CedarGroveStudios/RetroMeter/docs/input output ratio.pdf

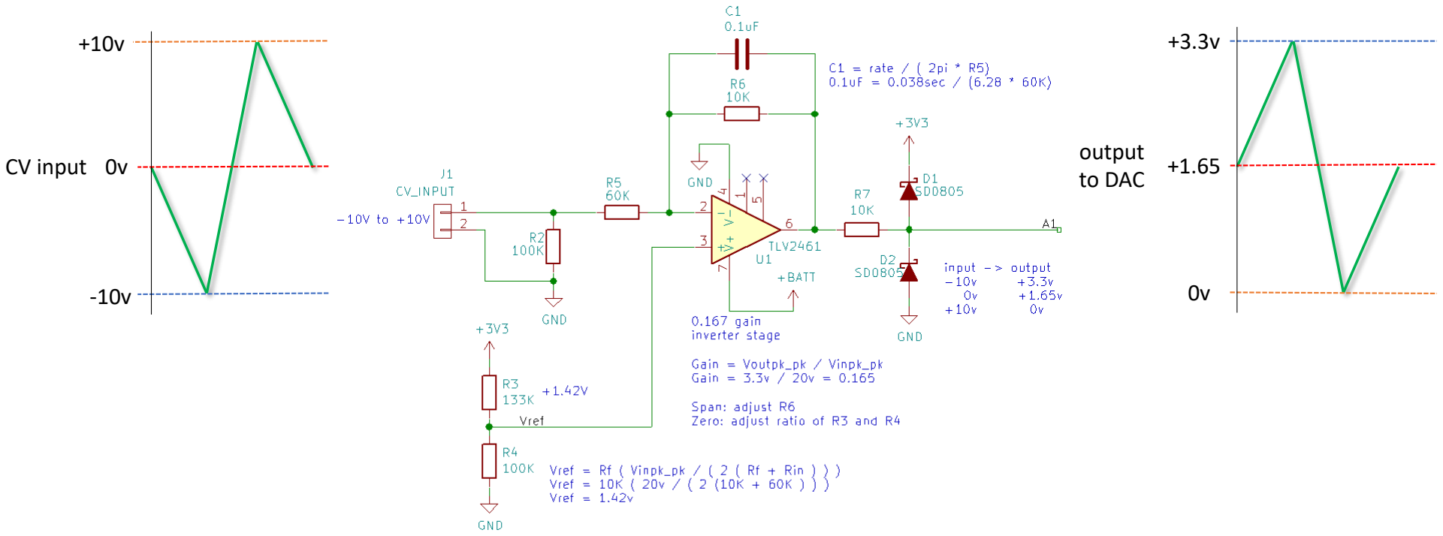
[picture p24: page 1]

+3.3v

+1.65

0v

output
to DAC

-10v

0v

+10v

CV input
