CedarGroveStudios/RetroMeter/docs/retro meter v02.pdf

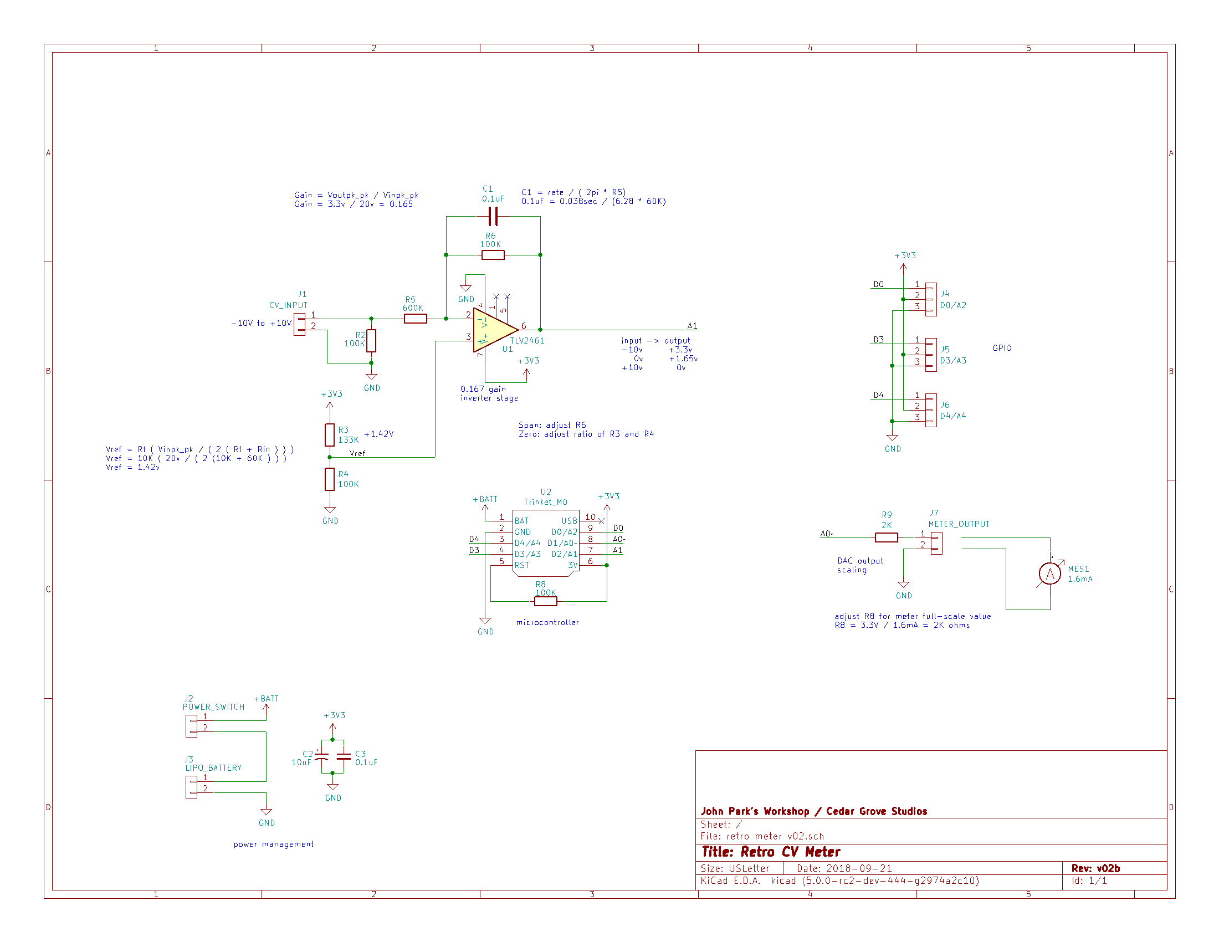
[picture p25: page 1]
