CedarGroveStudios/RetroMeter/docs/2018-08-17 retro meter study/schematic v01.pdf

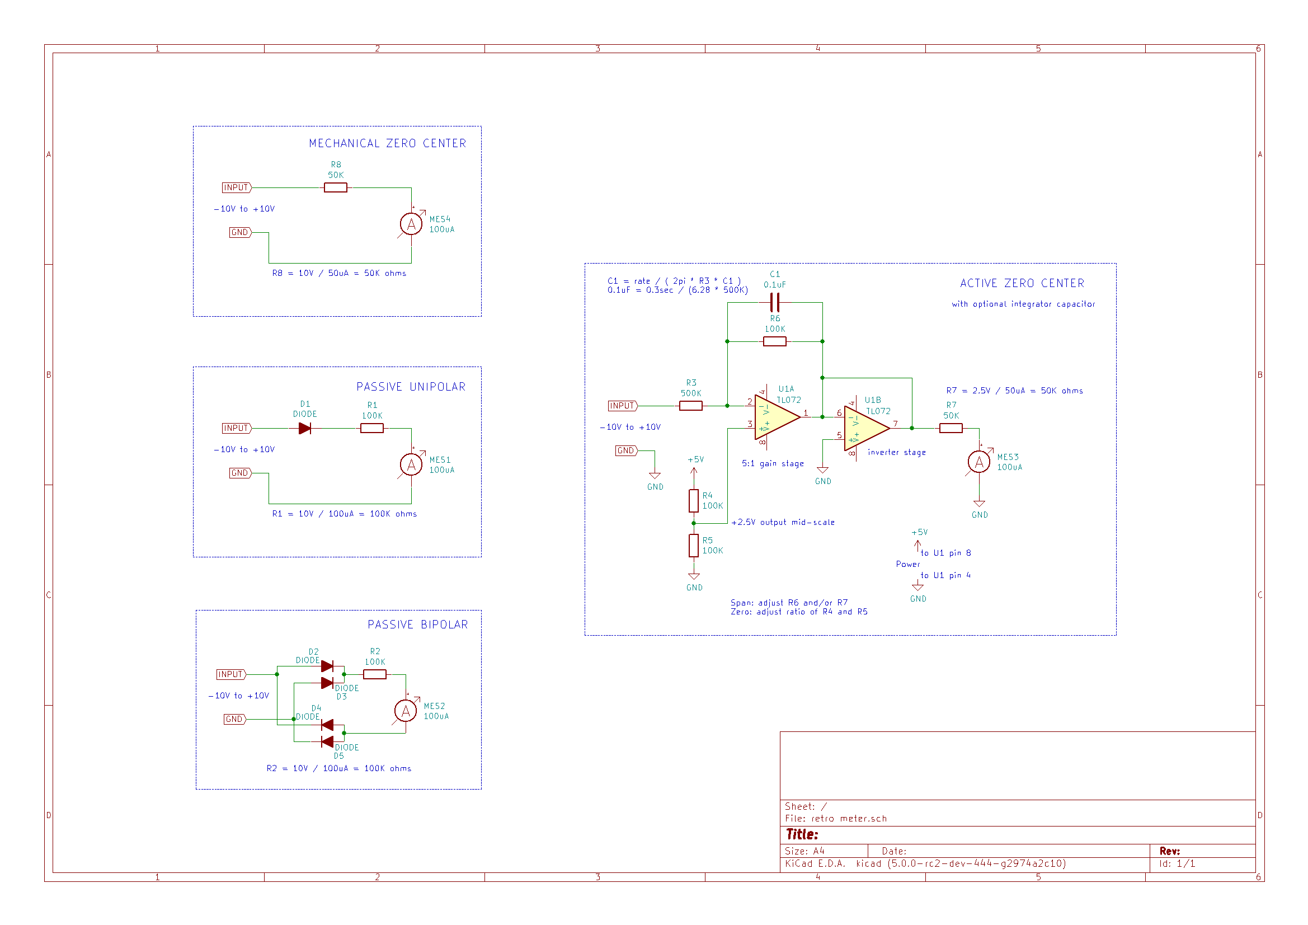
[picture p26: page 1]
