CedarGroveStudios/RetroMeter/docs/2018-08-17 retro meter study/original meter circuit.PNG

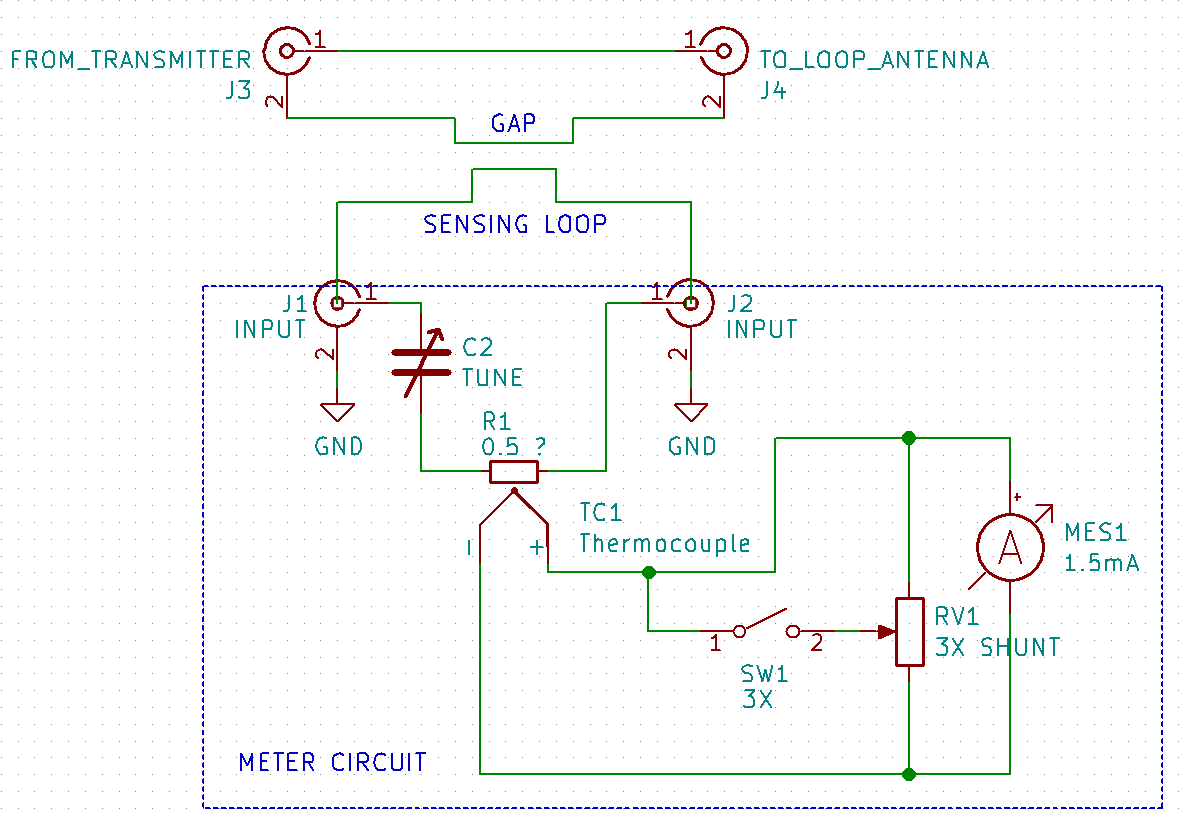
docs/2018-08-17 retro meter study/original meter circuit.PNG
