CedarGroveStudios/RetroMeter/docs/input output ratio.png

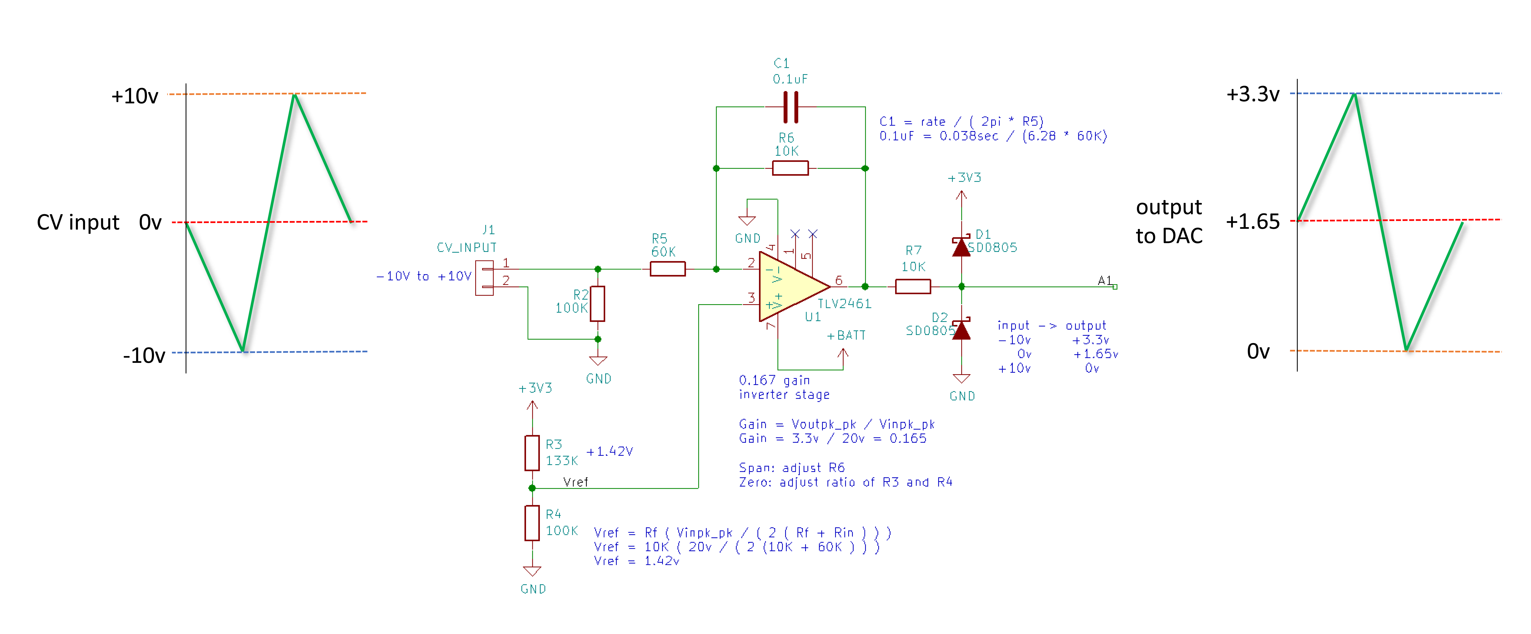
docs/input output ratio.png
