CedarGroveStudios/RetroMeter/PCB Rover/2018-08-20 analog Trinket sub front.png

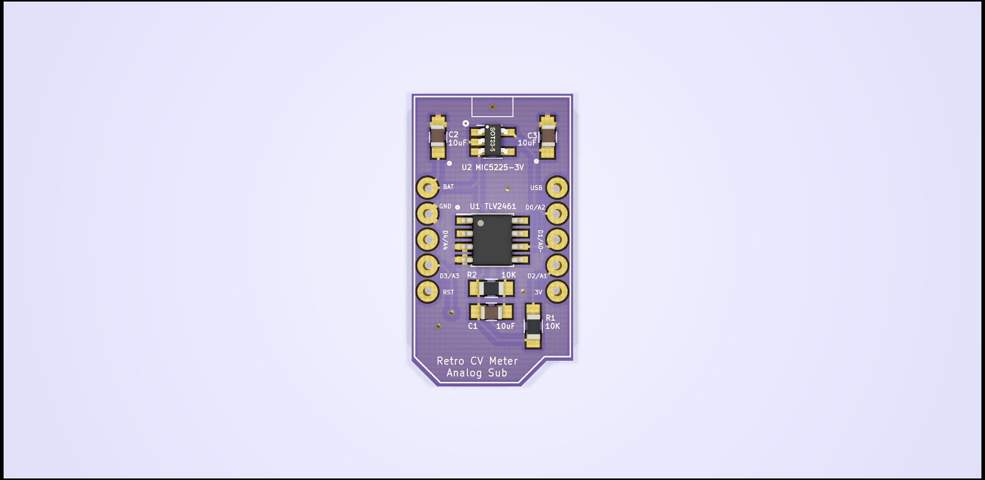
PCB Rover/2018-08-20 analog Trinket sub front.png
