CedarGroveStudios/RetroMeter/photos/DSC05513a lores.jpg

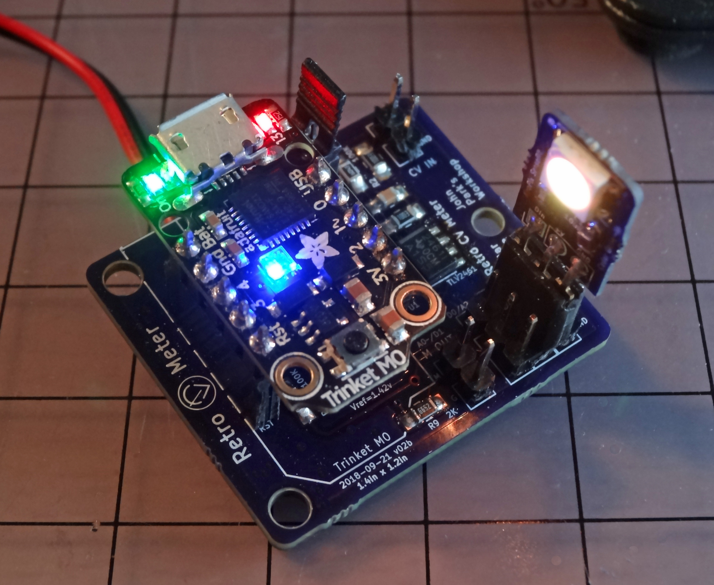
photos/DSC05513a lores.jpg
