CedarGroveStudios/RetroMeter/photos/DSC05515a lores.jpg

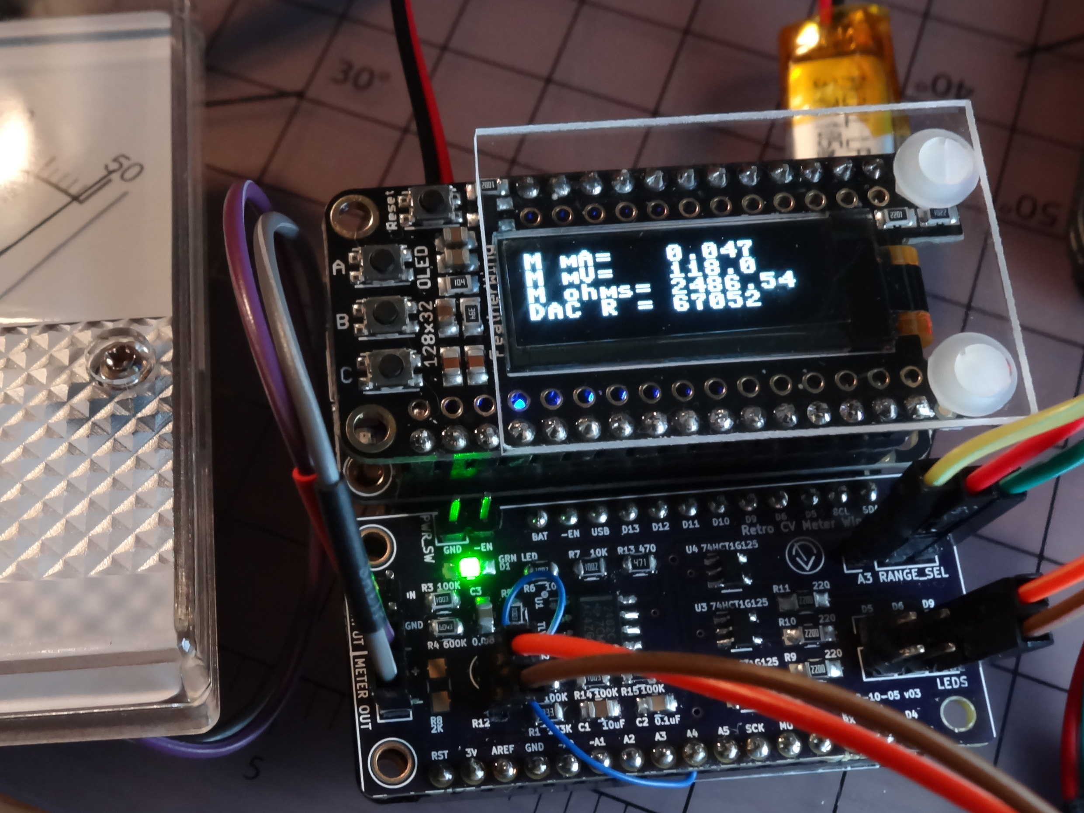
photos/DSC05515a lores.jpg
