CedarGroveStudios/RetroMeter/photos/IMG_0112a.jpg

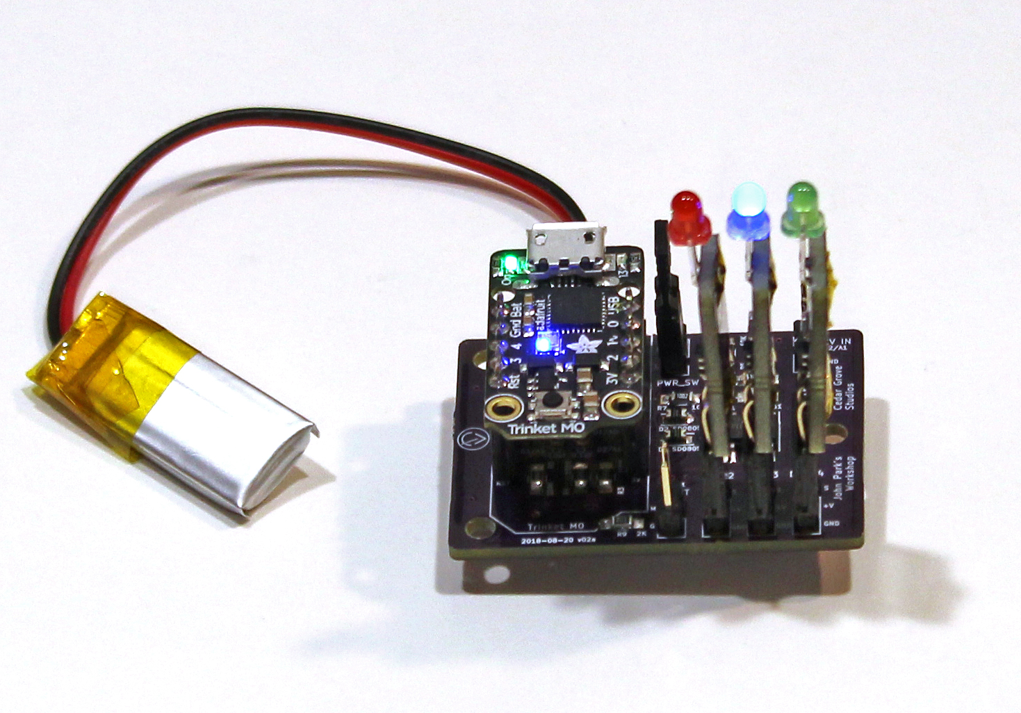
photos/IMG_0112a.jpg
