CedarGroveStudios/RetroMeter/photos/retro meter v02 iso top act.png

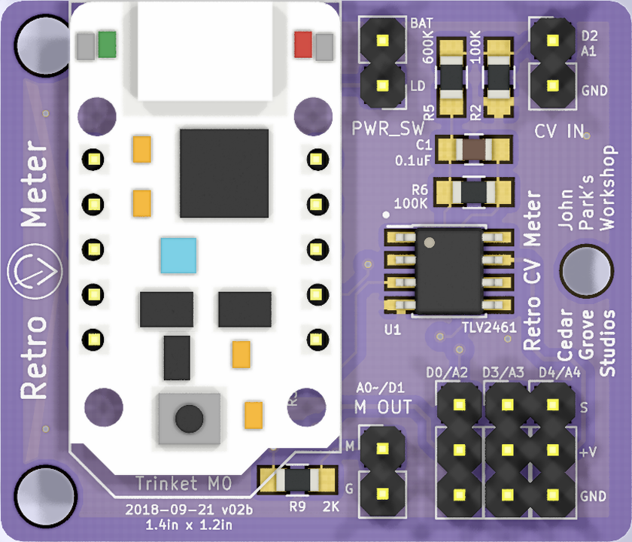
photos/retro meter v02 iso top act.png
