CedarGroveStudios/RetroMeter/photos/retro meter v02 iso top.png

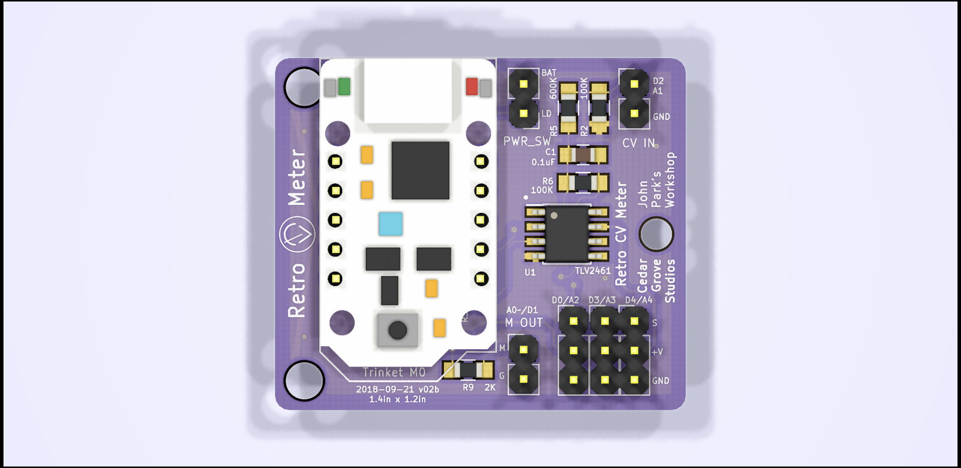
photos/retro meter v02 iso top.png
