CedarGroveStudios/RetroMeter/photos/retro meter v02 pins top.png

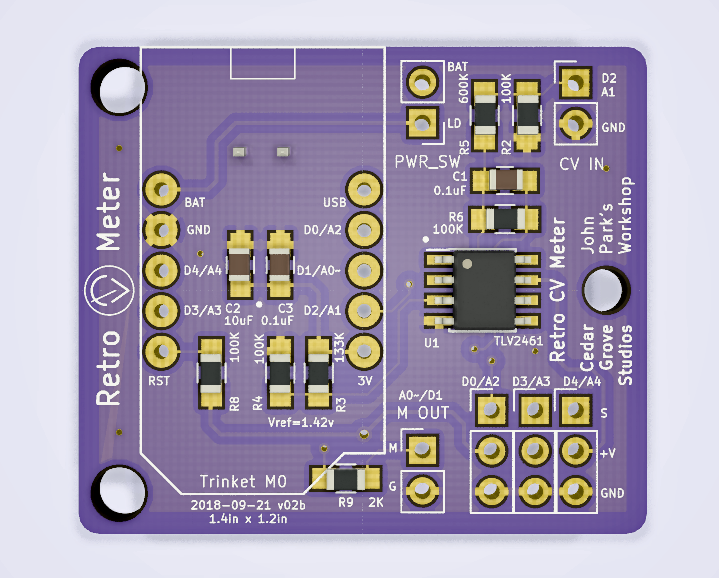
photos/retro meter v02 pins top.png
