CedarGroveStudios/RetroMeter/photos/retro meter v03 pinout bottom.png

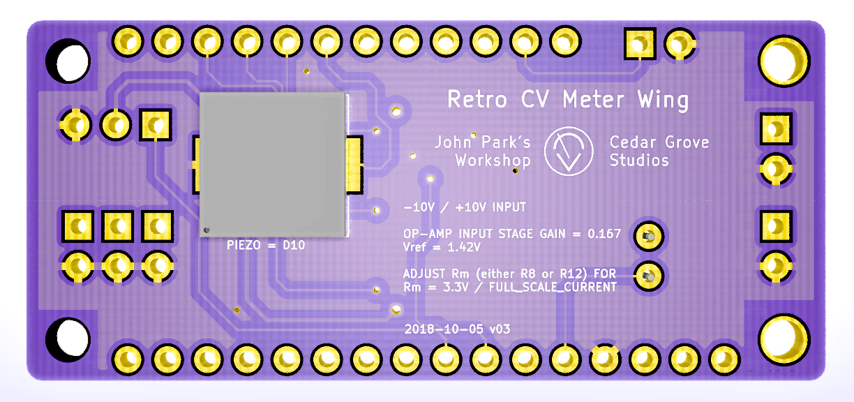
photos/retro meter v03 pinout bottom.png
