CedarGroveStudios/RetroMeter/photos/screen cap.jpg

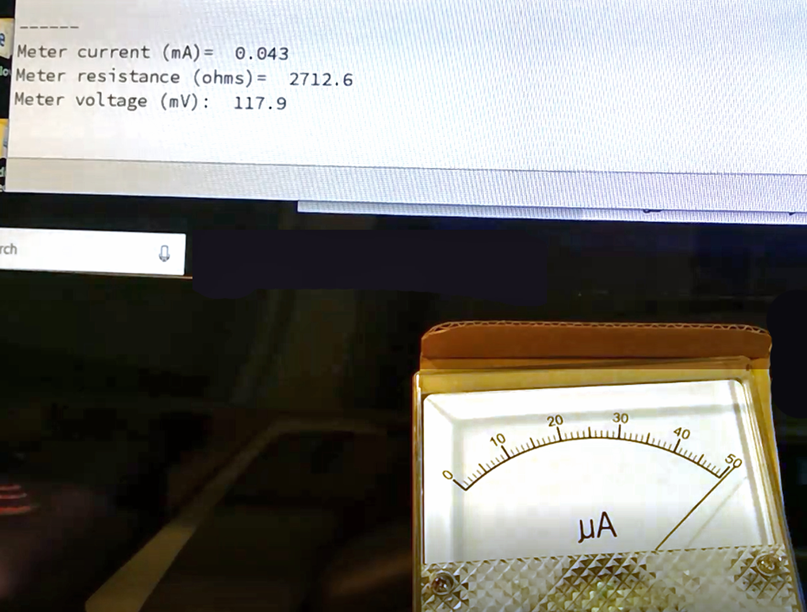
photos/screen cap.jpg
