CedarGroveStudios/RetroMeter/docs/2018-09-05 meter tutorial/photos and drawings/1x77r protract.jpg

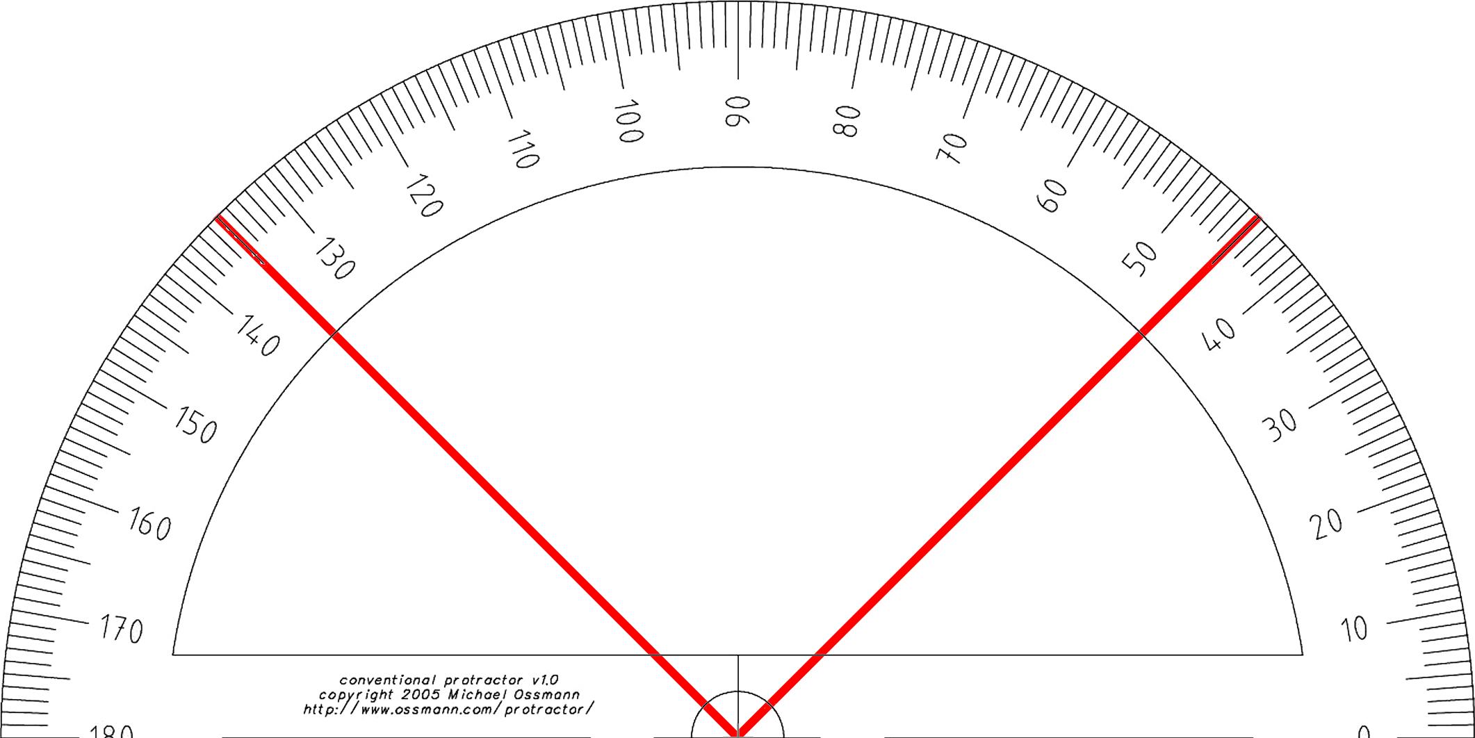
docs/2018-09-05 meter tutorial/photos and drawings/1x77r protract.jpg
