CedarGroveStudios/RetroMeter/docs/2018-09-05 meter tutorial/photos and drawings/conventional-protractor.jpg

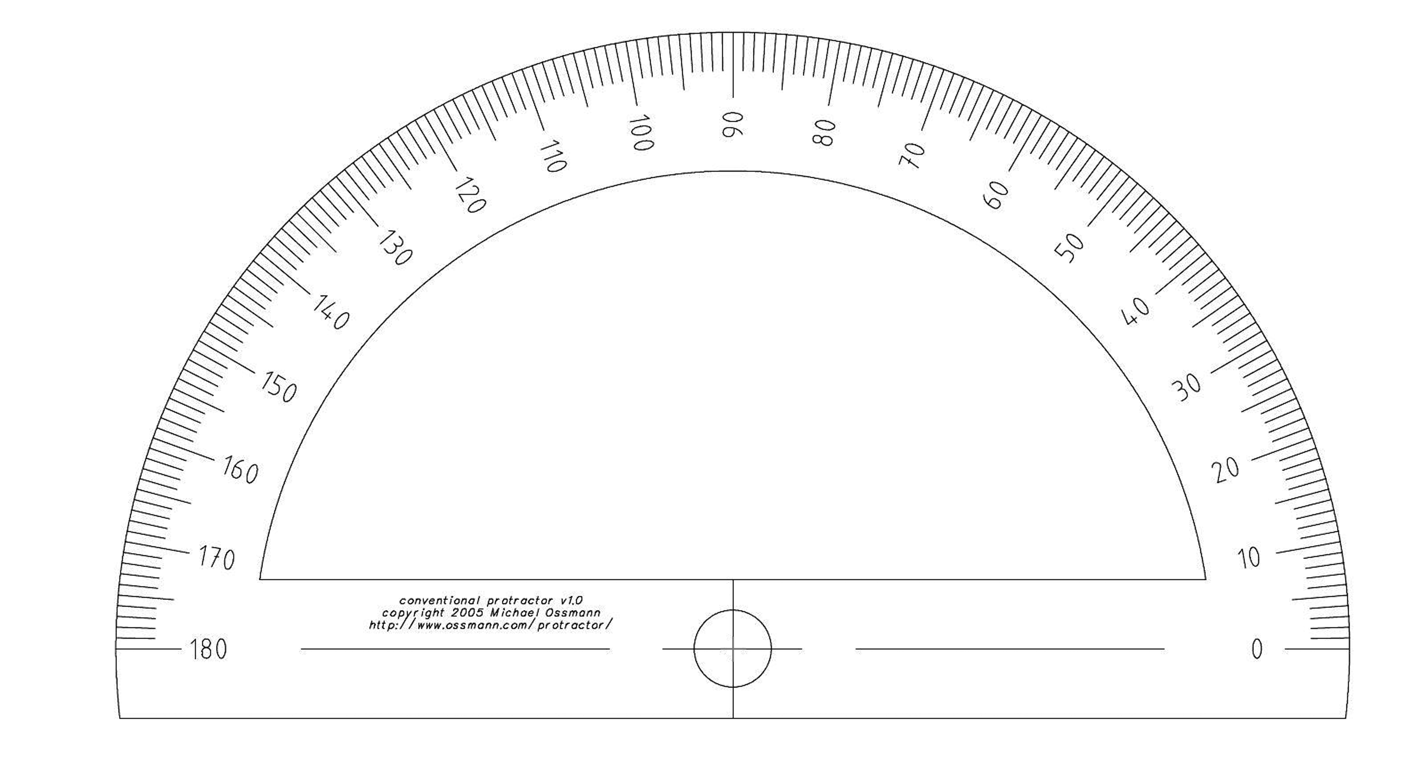
docs/2018-09-05 meter tutorial/photos and drawings/conventional-protractor.jpg
