CedarGroveStudios/RetroMeter/docs/2018-09-05 meter tutorial/photos and drawings/IMG_0385a annotated.jpg

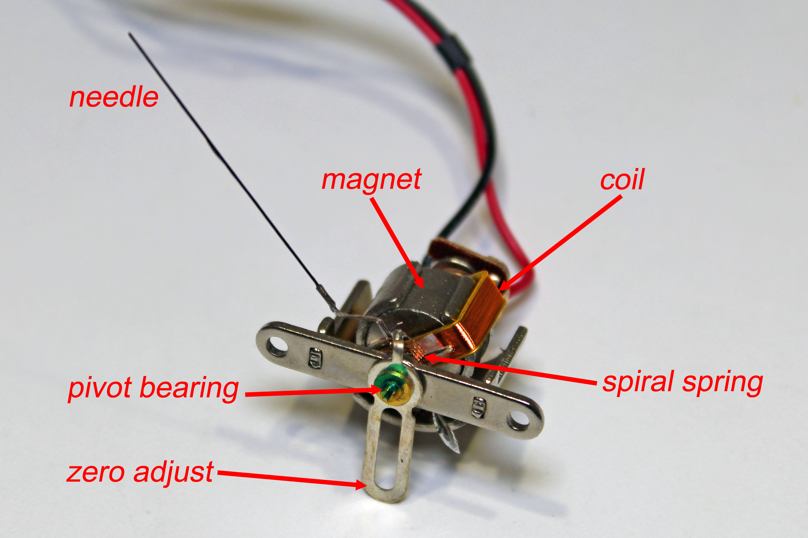
docs/2018-09-05 meter tutorial/photos and drawings/IMG_0385a annotated.jpg
