CedarGroveStudios/RetroMeter/docs/2018-09-05 meter tutorial/photos and drawings/meter center.bmp

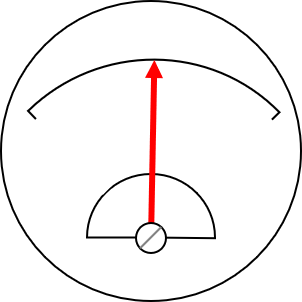
docs/2018-09-05 meter tutorial/photos and drawings/meter center.bmp
