CedarGroveStudios/RetroMeter/docs/2018-09-05 meter tutorial/photos and drawings/meter graphics all v3/Slide8.JPG

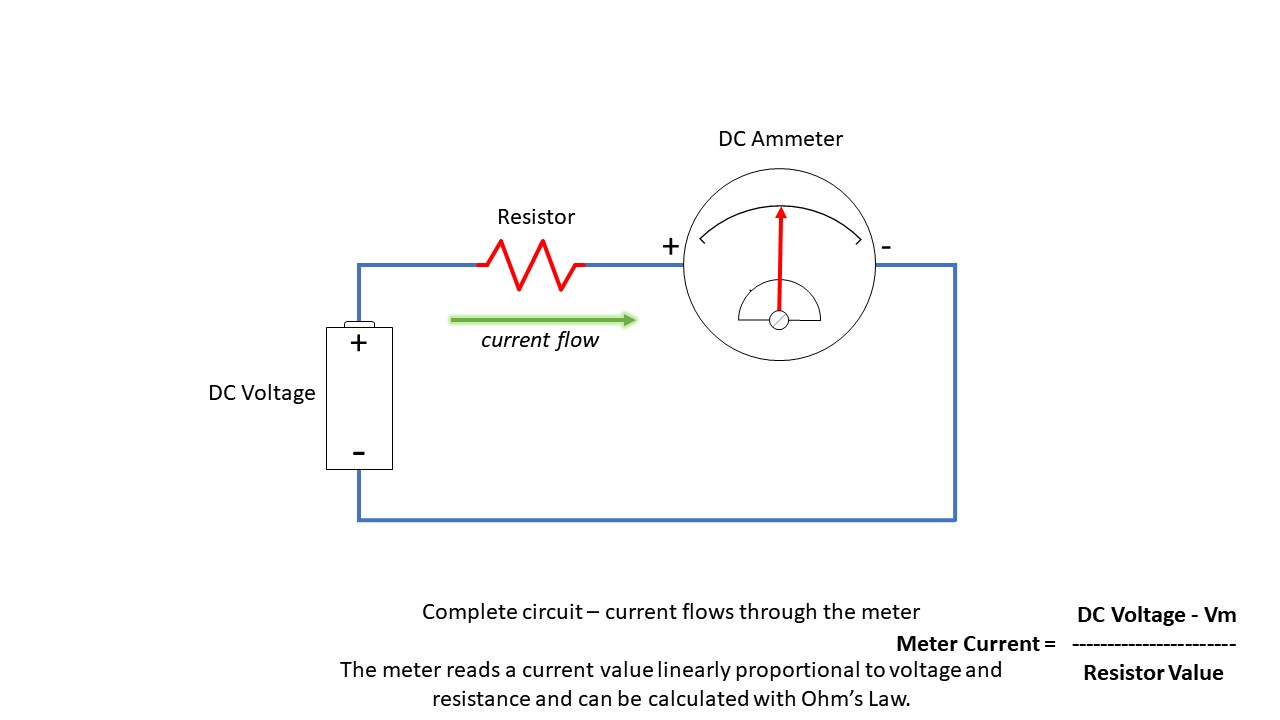
docs/2018-09-05 meter tutorial/photos and drawings/meter graphics all v3/Slide8.JPG
