CedarGroveStudios/RetroMeter/docs/2018-09-05 meter tutorial/photos and drawings/meter high.bmp

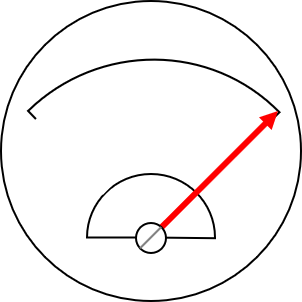
docs/2018-09-05 meter tutorial/photos and drawings/meter high.bmp
