CedarGroveStudios/RetroMeter/docs/2018-09-05 meter tutorial/photos and drawings/meter scale v02.jpg

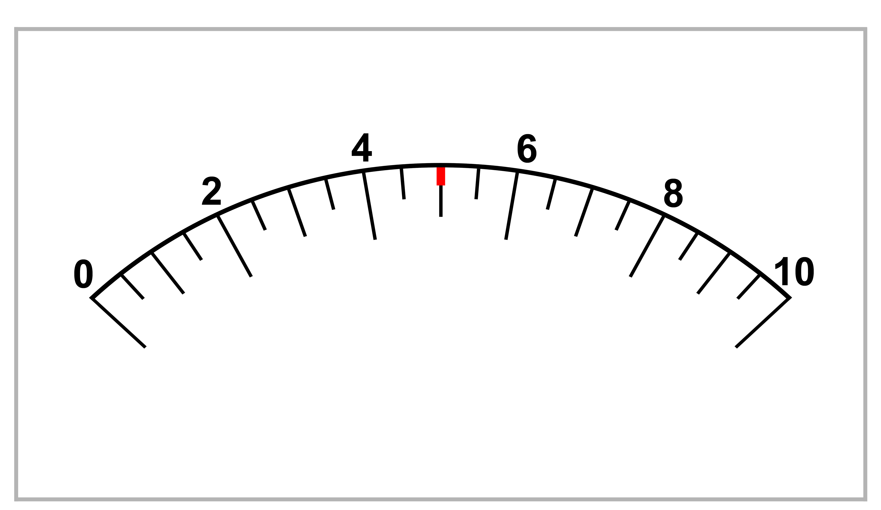
docs/2018-09-05 meter tutorial/photos and drawings/meter scale v02.jpg
