CedarGroveStudios/RetroMeter/docs/2018-09-05 meter tutorial/photos and drawings/Meter Tutorial 2018-11-12 v01_bba.jpg

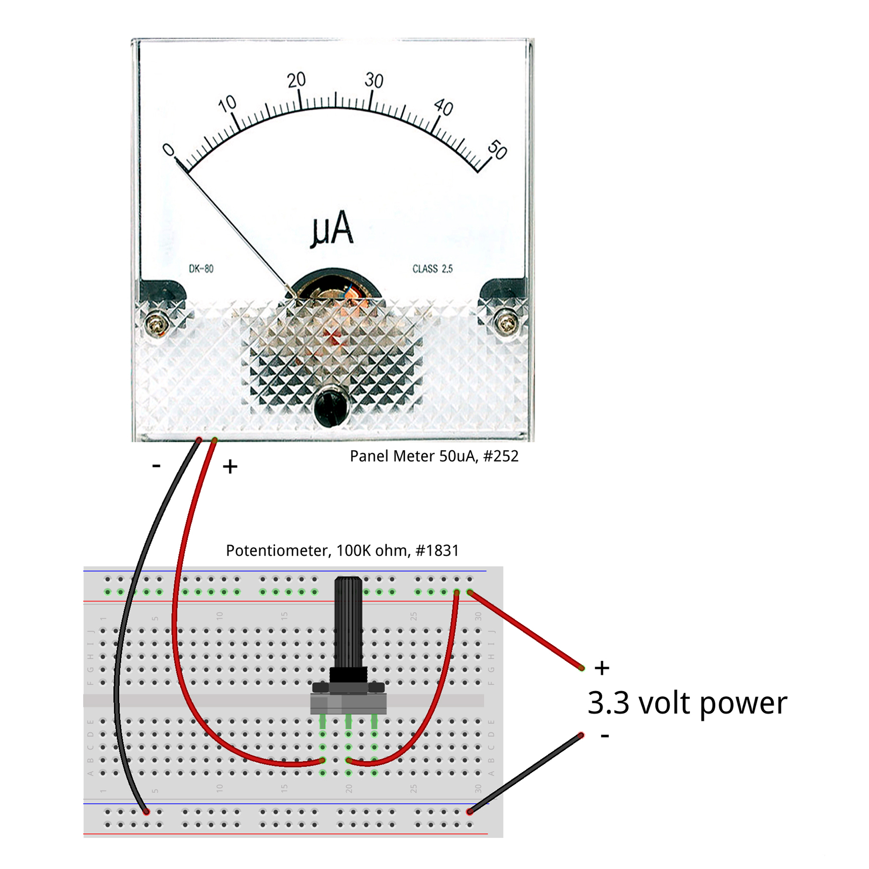
docs/2018-09-05 meter tutorial/photos and drawings/Meter Tutorial 2018-11-12 v01_bba.jpg
