CedarGroveStudios/RetroMeter/docs/2018-09-05 meter tutorial/photos and drawings/original meter circuit.PNG

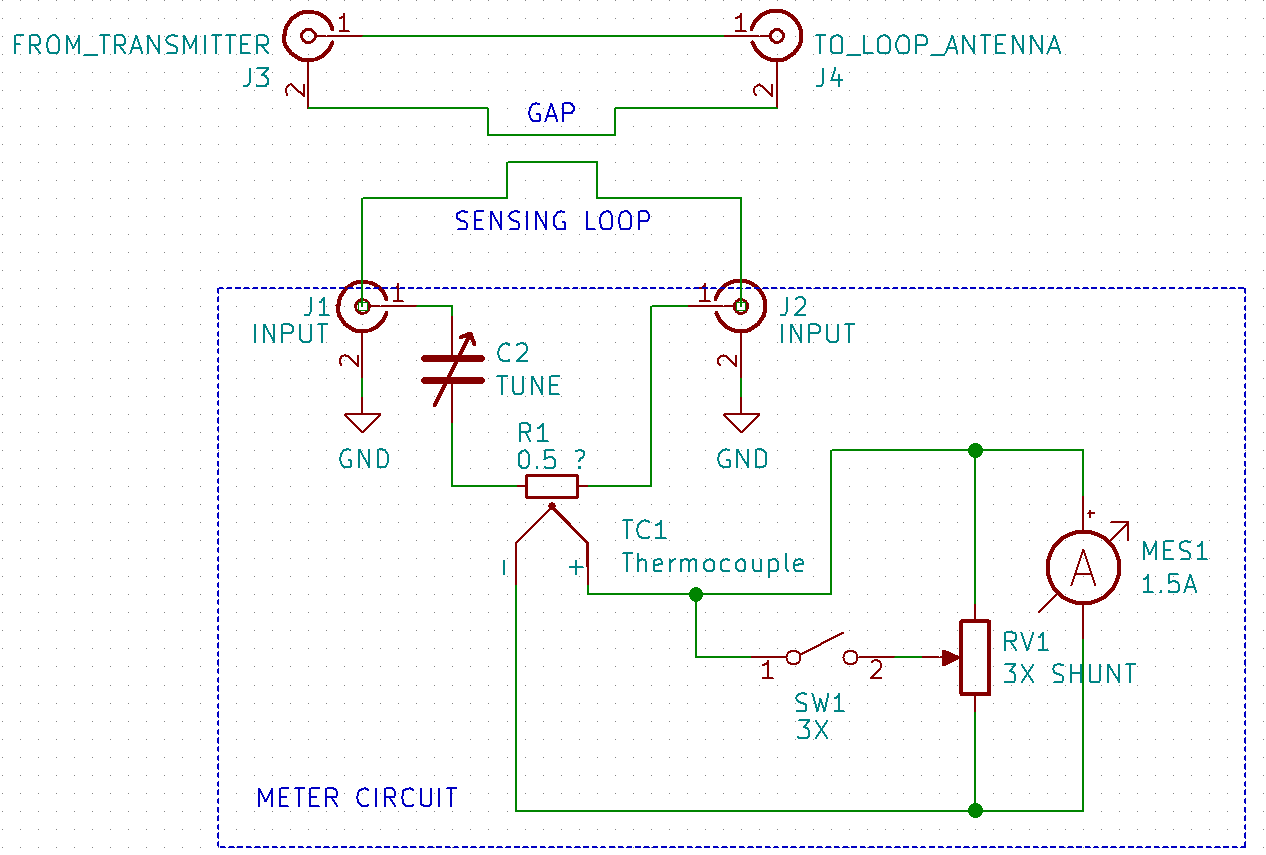
docs/2018-09-05 meter tutorial/photos and drawings/original meter circuit.PNG
