CedarGroveStudios/RetroMeter/docs/2018-09-05 meter tutorial/photos and drawings/Resistor 2_46 ohms DigiKey.PNG

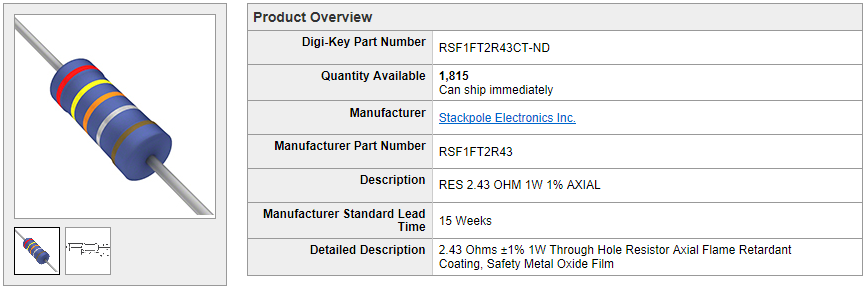
docs/2018-09-05 meter tutorial/photos and drawings/Resistor 2_46 ohms DigiKey.PNG
