CedarGroveStudios/RetroMeter/docs/meter tester schematic detail.PNG

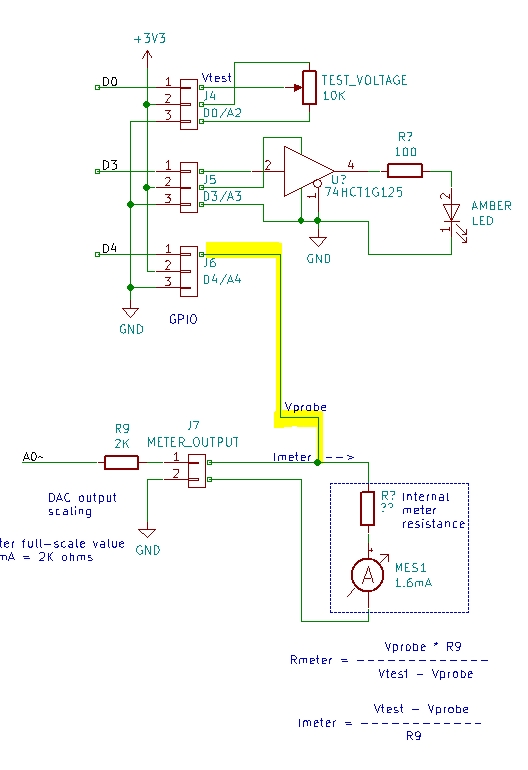
docs/meter tester schematic detail.PNG
