CedarGroveStudios/RetroMeter/PCB Rover/2018-08-20 analog Trinket sub.pdf

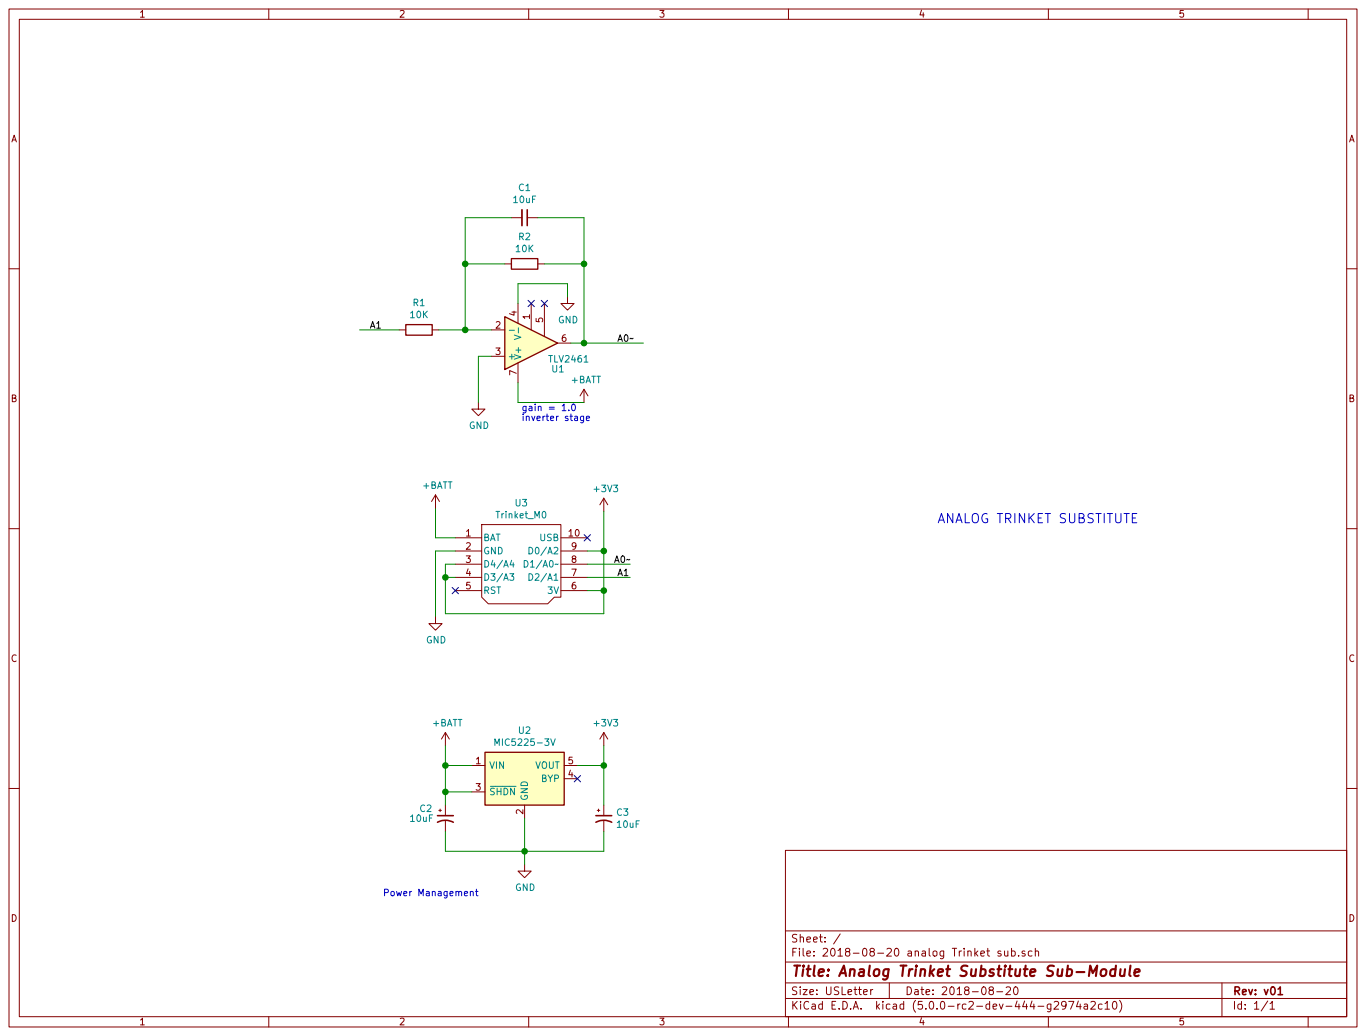
[picture p72: page 1]

7U1 TLV2461 A1 A0 BAT 1 USB 10 GND 2 D4/A4 3 D3/A3 4 RST 5

Id: 1/1 Title: Analog Trinket Substitute Sub-Module
