CedarGroveStudios/RetroMeter/PCB Breakout/Spice simulation/LTSpice simulation.asc

R2: res; 6K
R3: res; 1K
R5: res; 133K
R6: res; 100K
U1: LT1001
V1: voltage; 15
V2: voltage; SINE(0 10 10)
V3: voltage; 3.3
V5: voltage; -15
Named nets: 0, +V, -V, Vin, Vamp, Vref
.tran .3
Vref = R3 ( Vinpk-pk / ( 2 ( R3 + R2 ) ) )
Vref = 1K ( 20v / ( 2 ( 1K + 6K ) ) )
Vref = 1.42857v
